jack2bs/Many-Segment-Display/Code/USBTest.ioc

Mcu.UserName=STM32G441CBTx
PA11.Signal=USB_DM
PA12.Signal=USB_DP
